tradfree-mod/dimmer-frame/bottom-case.scad

include <config.scad>
include <include/sizes.scad>
include <include/modules.scad>
include <parts/main_body.scad>

mainBody();
