tradfree-mod/dimmer-frame/pcb-holder.scad

include <include/sizes.scad>

cube(pcb_holder_dimens);
